ThunderFly-aerospace/TFFLIP2PH/doc/gen/dxf/TFFLIP2PH-B_Courtyard.dxf

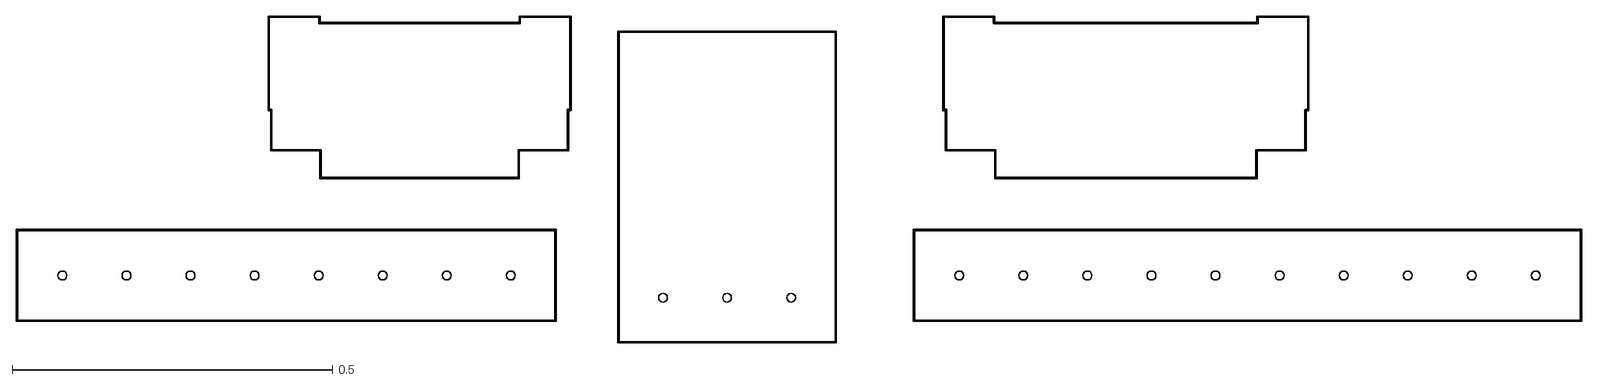
[picture p9: CAD file, 2026-01-07]
doc/gen/dxf/TFFLIP2PH-B_Courtyard.dxf
2.44 x 0.51
