ThunderFly-aerospace/TFFLIP2PH/doc/gen/dxf/TFFLIP2PH-F_Courtyard.dxf

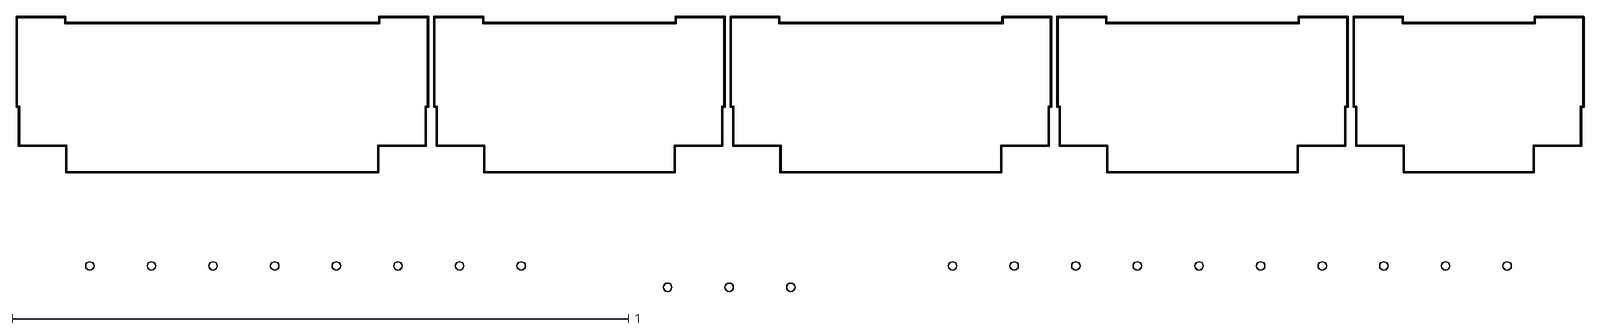
[picture p10: CAD file, 2026-01-07]
doc/gen/dxf/TFFLIP2PH-F_Courtyard.dxf
2.54 x 0.446
