ThunderFly-aerospace/TFFLIP2PH/doc/gen/dxf/TFFLIP2PH-Edge_Cuts.dxf

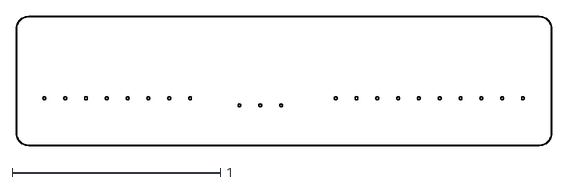
[picture p11: CAD file, 2026-01-07]
doc/gen/dxf/TFFLIP2PH-Edge_Cuts.dxf
2.57 x 0.62
