ThunderFly-aerospace/TFFLIP2PH/doc/gen/dxf/TFFLIP2PH-F_Fab.dxf

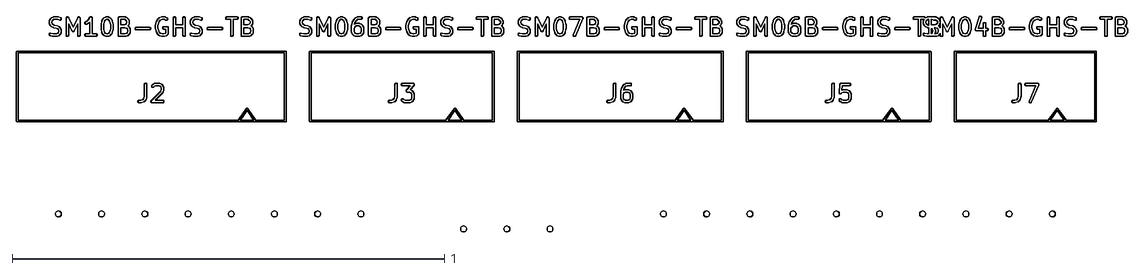
[picture p12: CAD file, 2026-01-07]
doc/gen/dxf/TFFLIP2PH-F_Fab.dxf
2.57 x 0.499
